Squonk42/TL-WR703N/3D/eagleUp_TL-WR703N_board_bottom.jpg

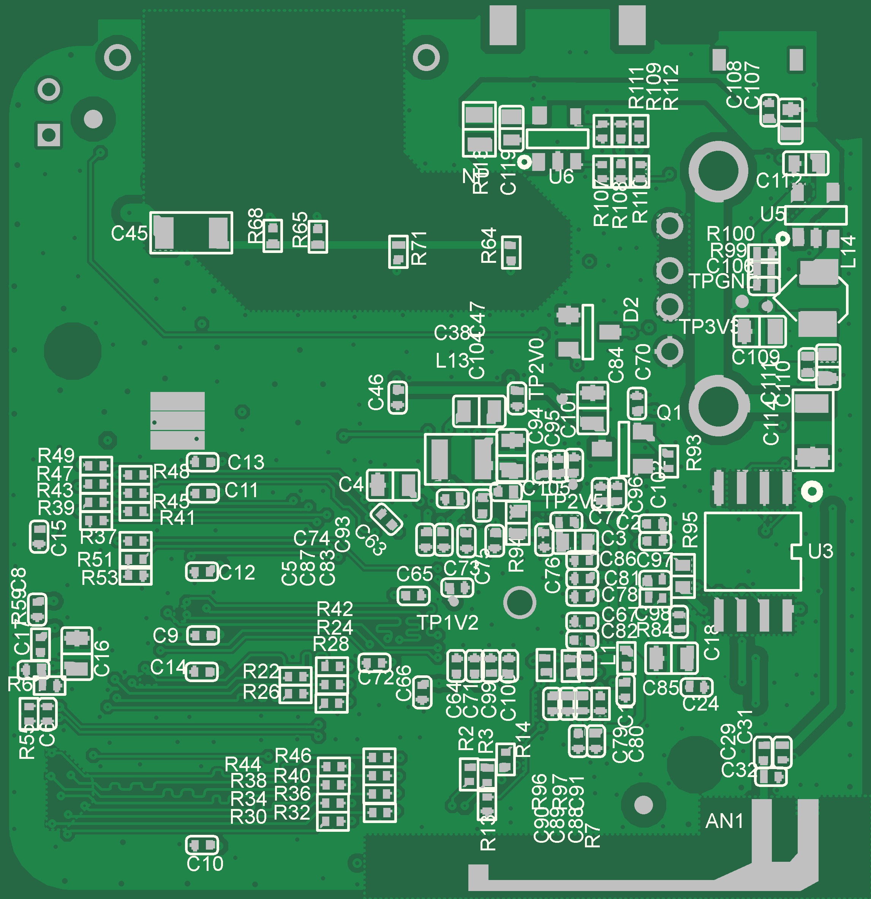
3D/eagleUp_TL-WR703N_board_bottom.jpg
