Squonk42/TL-WR703N/3D/eagleUp_TL-WR703N_imagesize.png

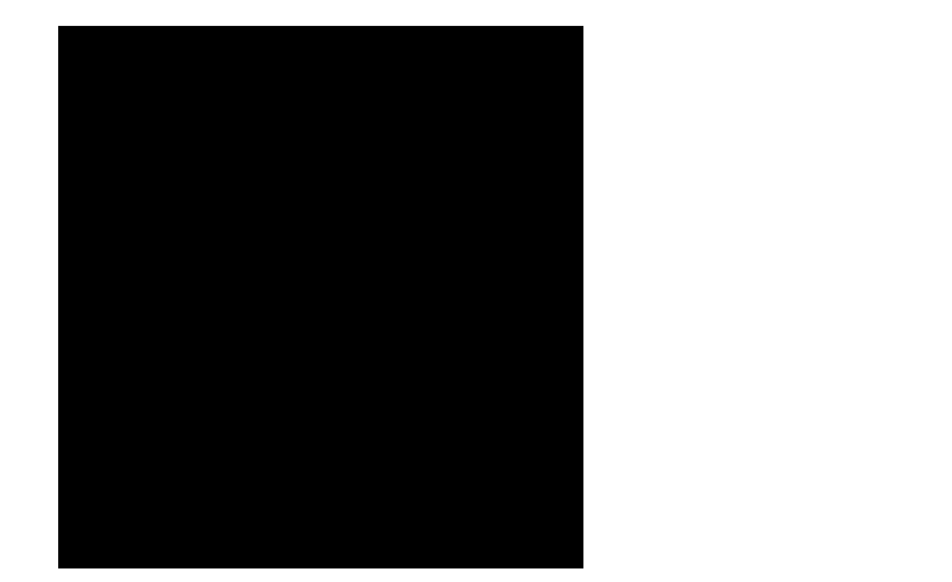
3D/eagleUp_TL-WR703N_imagesize.png
