Squonk42/TL-WR703N/3D/eagleUp_TL-WR703N_top_silk.png

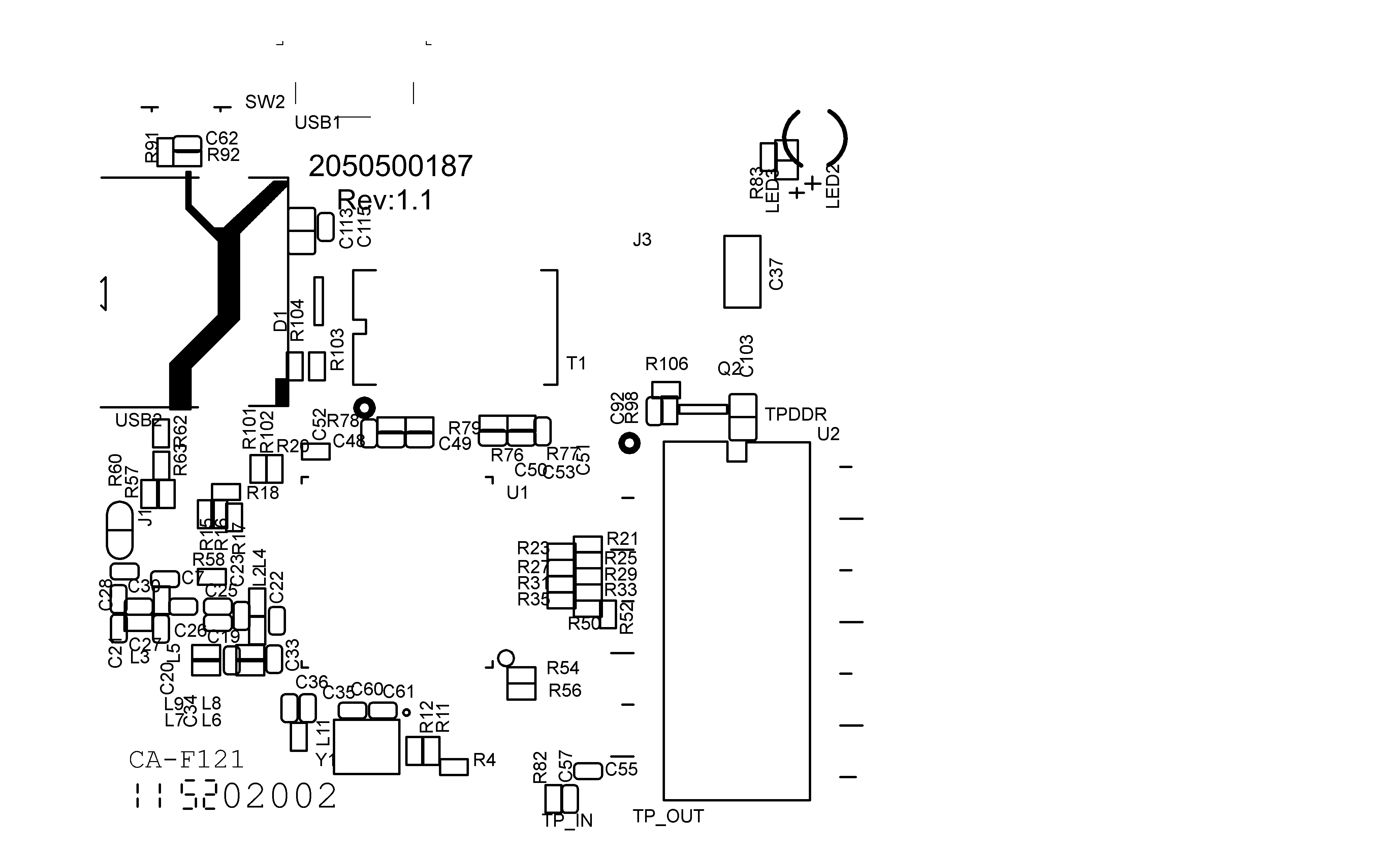
3D/eagleUp_TL-WR703N_top_silk.png
