Squonk42/TL-WR703N/Pictures/TL-WR703N Bare Board Top.jpg

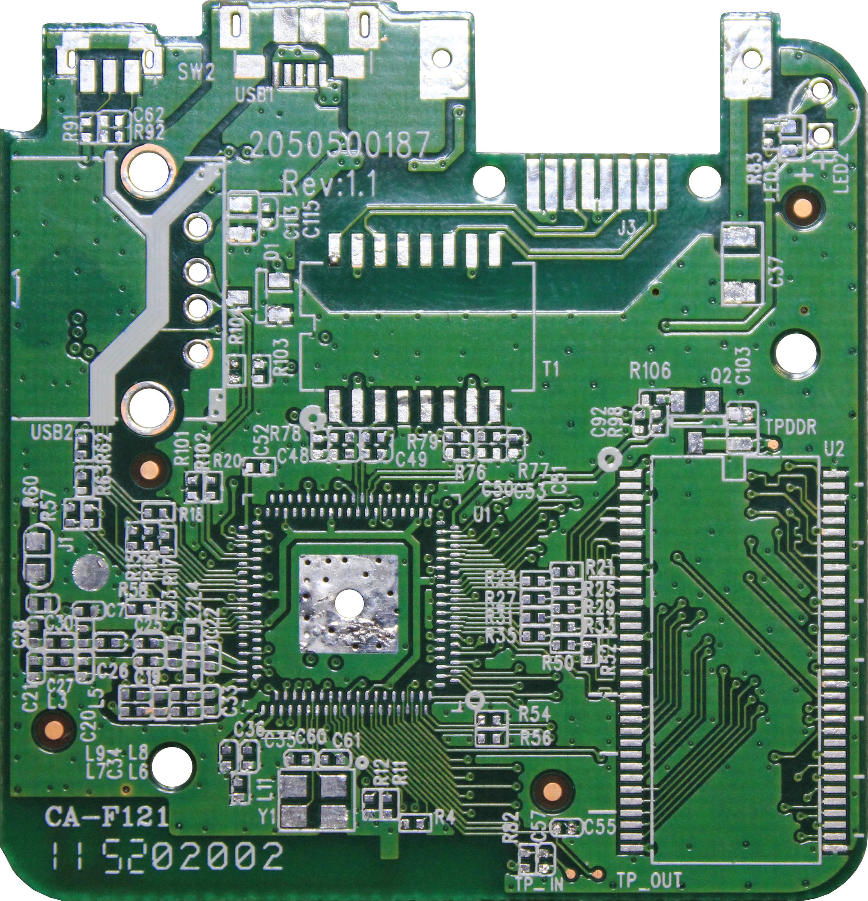
Pictures/TL-WR703N Bare Board Top.jpg
